solomon0256/Wireless-Charging-Receiver-Dock/result/pcb (1).png

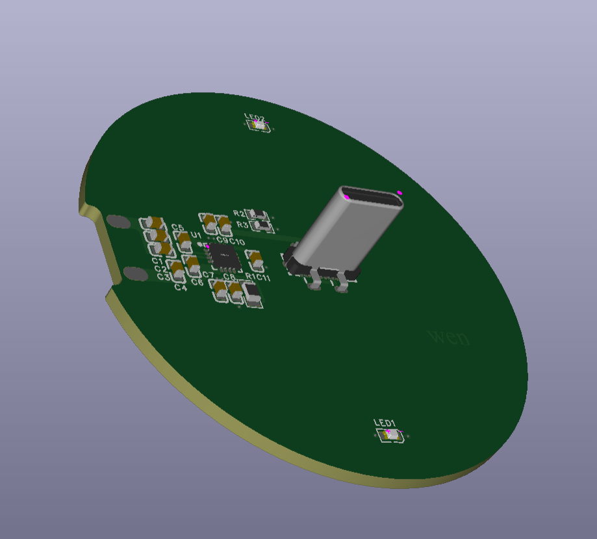
result/pcb (1).png
