solomon0256/Wireless-Charging-Receiver-Dock/result/pcb (2).png

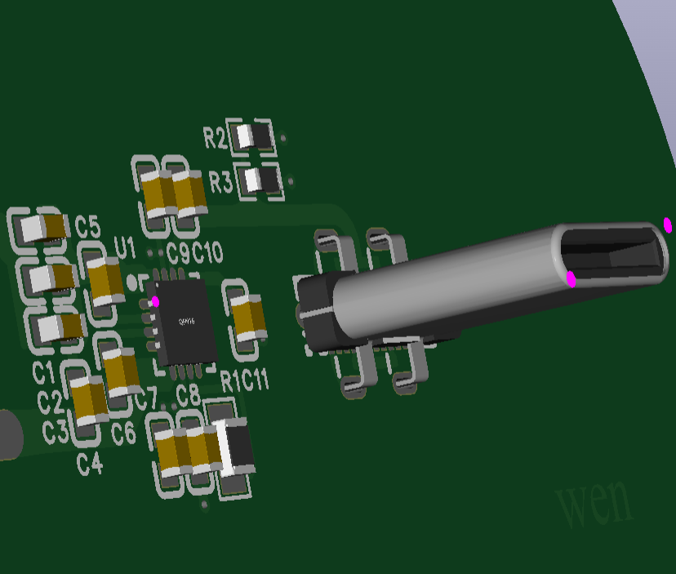
result/pcb (2).png
