solomon0256/Wireless-Charging-Receiver-Dock/result/pcb (3).png

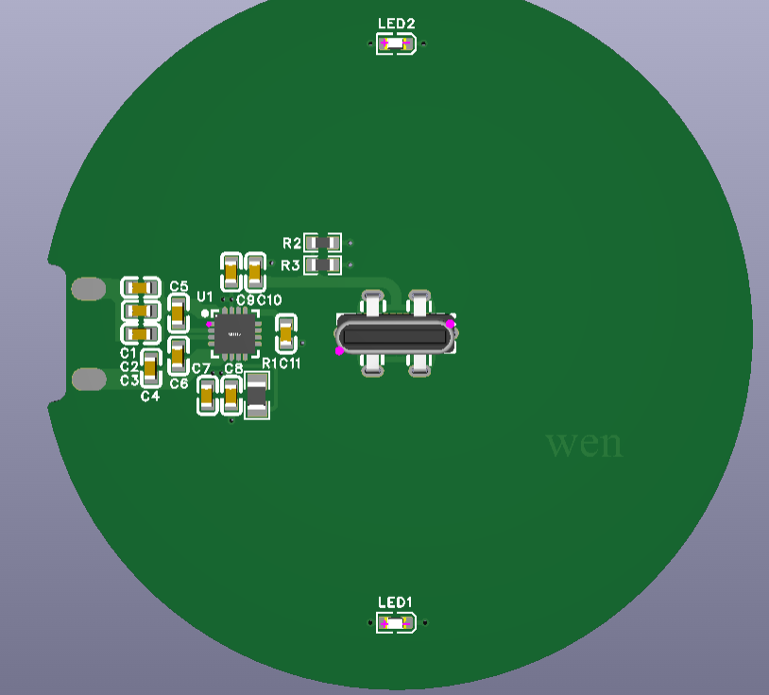
result/pcb (3).png
