solomon0256/Wireless-Charging-Receiver-Dock/result/pcb (4).png

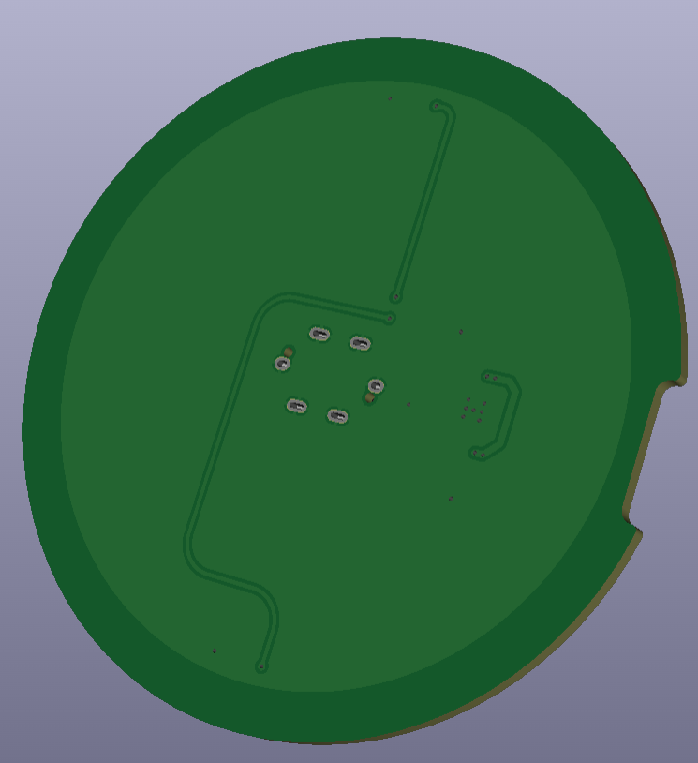
result/pcb (4).png
