solomon0256/Wireless-Charging-Receiver-Dock/result/pcb (5).png

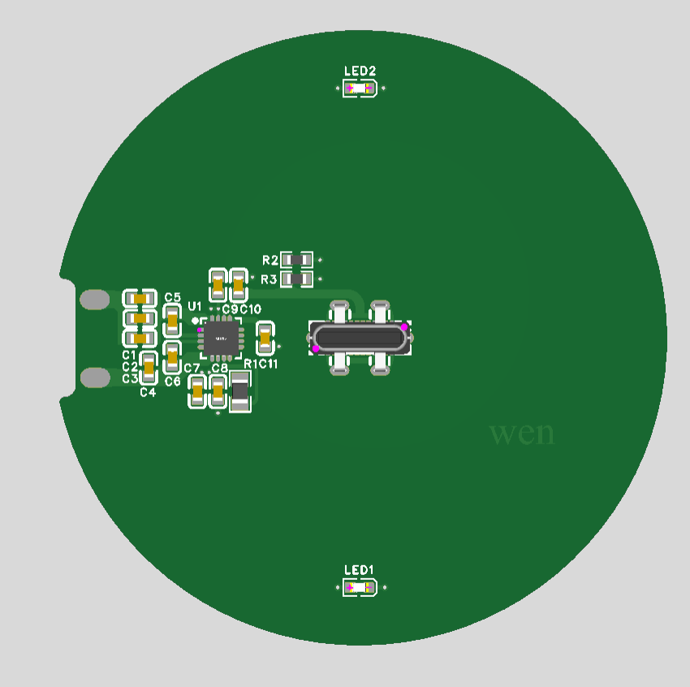
result/pcb (5).png
