solomon0256/Wireless-Charging-Receiver-Dock/result/pcb (6).png

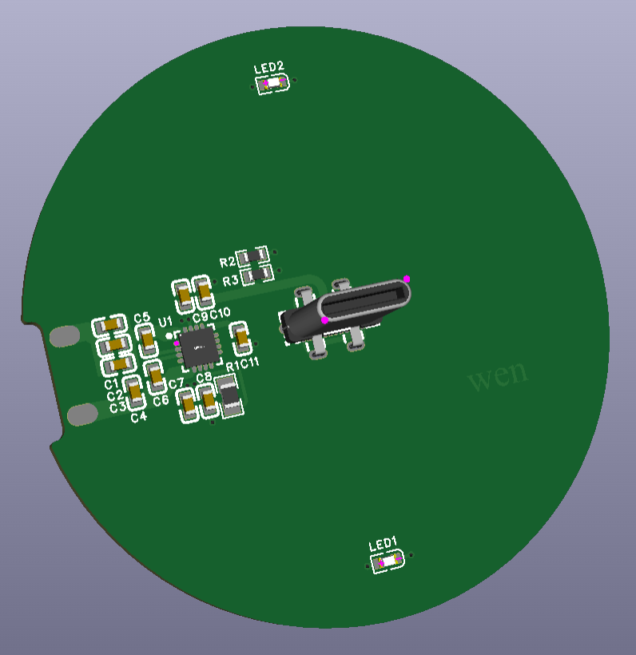
result/pcb (6).png
